engmung/Patternflow/firmware/CUSTOM_PATTERNS.md

# Custom Patterns

Patternflow includes a workflow for creating patterns without writing low-level rendering code. Two paths converge in the same place — the Live Editor at [patternflow.work](https://patternflow.work) → **Pattern** section → **Live Editor**.

- **AI-assisted** — describe the pattern in plain language, paste the AI's output into the editor, tune knobs, copy to C++, flash. No shader knowledge required.
- **Direct** — write the JavaScript pattern by hand in the editor, then convert to C++. For anyone comfortable with fragment-shader-style code.

> **New: you no longer need the Arduino IDE.** The last step — turning a pattern into firmware and getting it onto the board — now runs in the browser: the server compiles, your browser flashes over USB. See [step 5](#5-convert-to-c-and-flash). A local build is still the route for firmware development itself; that is PlatformIO through `firmware/bundles/build.sh`, not the Arduino IDE (the IDE cannot build the editions' library set).

> **Newer still: patterns can install without any flashing at all.** On firmware
> with loadable-module support, the same `.h` builds into a tiny `.pfm` module
> that installs over Wi-Fi from the device's `/patterns` page — a few KB, no
> reflash, no reboot, unlimited slots. The community cart does this end to end.
> Details: [firmware/README.md → Loadable pattern modules](README.md#loadable-pattern-modules-pfm).

The 5-step path below is the AI-assisted route. The direct route reuses the same editor; skip to [Direct coding](#direct-coding-no-ai) if you don't need AI help.

---

## The 5-step path

### 1. Open the Live Editor

Go to [patternflow.work](https://patternflow.work), scroll to the **Pattern** section, and click **Live Editor**. You'll see a 3D preview of the panel on one side and a code editor on the other.

### 2. Copy the creation prompt

Click **Copy creation prompt** above the editor. This copies a prompt that teaches the AI Patternflow's pattern API — the 128×64 grid, the four encoder inputs, the namespace structure, the render call. You don't need to read it. Just paste it.

### 3. Ask an AI for the pattern

Paste the prompt into Claude, ChatGPT, Gemini, or any other code-capable model. At the bottom of the prompt, describe what you want. Examples that have worked well:

- *"A slow vertical aurora — soft greens and purples, gentle wave motion, no hard edges."*
- *"Concentric rings expanding from the center, each ring a slightly different hue."*
- *"Plasma flow that looks like ink in water, deep blues bleeding into magentas."*
- *"A grid of dots pulsing in waves, like a stadium crowd doing the wave."*

The more visual and specific, the better. References to paintings, films, weather, or natural phenomena work well — AI models handle them.

### 4. Paste the JS into the editor

The AI returns JavaScript code. Paste it into the editor pane. The 3D preview updates immediately. The four on-screen knobs and the **ESP32 cost** readout at the top are live.

Turn the knobs to feel how the pattern responds. Adjust constants in the code directly — sensitivity, color ranges, motion speed — until it looks the way you want. This is where you make the pattern yours, not the AI's.

### 5. Convert to C++ and flash

When you're happy with how it looks:

1. Click **Copy C++ prompt**. This bundles your final JS together with a conversion prompt and copies the whole thing to your clipboard.
2. Paste into your AI assistant again. It returns C++ in Patternflow's namespace format.
3. Put it on the device. **Two routes, same result** — pick either:

#### Route A — from the browser (nothing to install, no cable)

In **Pattern Lab**, press **To hardware**, paste the C++ your assistant returned, then press **Apply to my Patternflow**. A server compiles just that pattern into a loadable module (`.pfm`, a few KB, about half a second) and your browser hands it to the board over Wi-Fi. It appears in the pattern list immediately — no reflash, no reboot, no USB.

No Arduino IDE, no board package, no editing `pattern_registry.h`. A community pattern already marked `.h` skips steps 1–2 entirely and offers **Send to my Patternflow**.

Requirements: the device powered on and on the same Wi-Fi as your computer. (Baking a pattern into a whole firmware image used to be the route here; it took fifteen seconds and a cable to do what this does in one, and it is gone. Updating the firmware itself is now its own flow — the device's console tells you when a release is newer and links to [patternflow.work/update](https://patternflow.work/update).)

If the build fails you get the compiler's own error. The usual causes are a helper the firmware already provides being redefined, or a type that differs from the JavaScript original.

#### Route B — a local build (PlatformIO)

1. Save the C++ output as `preset_yourname.h` inside `firmware/patternflow/presets/`.
2. Open `pattern_registry.h` and add two lines (see [Installing your pattern](#installing-your-pattern) below).
3. Build and flash with the bundled toolchain: `./firmware/bundles/build.sh flash patternflow.local` (over Wi-Fi) or `cd firmware/patternflow && pio run -t upload` (USB).

Still the route for changing anything beyond a pattern — firmware development, config edits, working offline, or building for a board you cannot plug into this machine.

> Install the ESP32 board package at **2.0.x**, not the latest 3.x: the newer core takes ~71 KB more internal RAM before your sketch starts, which is enough to stop large patterns loading. `firmware/patternflow/platformio.ini` pins the right core and installs the libraries for you (`cd firmware/patternflow && pio run -t upload`). See [firmware/README.md](README.md#required-board-package).

Long-press encoder 4 on the device to cycle to your new pattern.

> Route B flashes a **whole firmware image**, replacing the firmware and the presets compiled into it; Route A installs a module and touches nothing else. Any `.pfm` modules you've installed live on a separate FATFS partition and **survive a normal reflash** — they only go away if you enable *Erase All Flash Before Sketch Upload*, or format the partition from `/patterns`.

---

## The cost score, explained

At the top of the editor:

```
ESP32 cost: MEDIUM · score 16 · per pixel: trig 4, pow 0, sqrt 0, atan2 0
```

This counts expensive math operations in your pixel loop:

- **trig** — `sin`, `cos`, `tan` calls. Each adds real CPU cost per frame.
- **pow** — exponentiation. Expensive.
- **sqrt** — square root. Expensive.
- **atan2** — angle from x/y. The single most expensive common operation.

**The score is a signal, not a verdict.** It flags patterns that *might* slow down, but the actual frame rate depends on more than this count — loop structure, branching, how the ESP32's cache responds to your access pattern. In practice some patterns with high scores run smoothly, and some with moderate scores stutter unexpectedly.

The rough shape from experience: scores under 20 are reliably smooth. Patterns with truly heavy per-pixel math — stacked `sqrt`, multiple `atan2`, large `pow` — are where slowdowns reliably appear, typically well above score 50. Between those two zones, run it and see. The 3D preview in the browser is a hint, but the only honest test is on the device.

If your score climbs higher than you'd like, the most common fix is moving expensive math *out* of the pixel loop — a `sin` that depends only on time (not on x or y) can be computed once per frame and reused for all 8,192 pixels, and anything that depends only on x, y, or a constant can be precomputed into a lookup table in `setup()` and indexed in `draw()`. Tables are the cheap resource here: measured on hardware, static tables from 0 to 64 KB all render at the same frame rate — and on one real soliton pattern, replacing two `cosh` calls per pixel with a 4 KB table took it from 18 to 33 fps. You can also tell the AI directly: *"Keep cost score under 30. No `atan2`."* Models follow these constraints if you state them in the prompt.

One class of pattern deserves a note because it used to look impossible: anything built on `cosh`/`sinh`/`erf` (solitons, gaussian falloffs) failed to *load* on firmware before v3.5.2 — not slow, refused, with `unresolved symbol` in `loadError`. Those names all resolve now, and the build tooling catches any future gap before a pattern reaches a device. If a pattern of yours was written off as too heavy for the board, try it again on current firmware.

Note that the score measures the *JavaScript* as written — the C++ conversion prompt ships a decision table of firmware fast paths (precomputed per-pixel radius/angle tables for fixed-center patterns, `PFMath::fastAtan2`, cell-hash and pow LUTs), so a HIGH-scoring radial pattern often converts to cheap C++ anyway. Treat the score as pressure, not a wall.

---

## Installing your pattern

Drop the generated header file into the firmware folder:

```
firmware/patternflow/
├── patternflow.ino
├── config.h                   ← hardware pins / display / limits / LED calibration
├── net_config.h               ← Wi-Fi / OTA defaults (+ feature tuning defaults)
├── patternflow_secrets.example.h  ← copy to patternflow_secrets.h for credentials
├── pattern_registry.h         ← edit this
├── _TEMPLATE.h                ← starting point for a new preset
├── presets/                   ← the curated patterns; 35 files, all named preset_*.h
│   ├── preset_origin.h        ← the one compiled into firmware.bin
│   ├── preset_wave_saw.h      ← …the rest ship as the Basics pack (web/public/packs/)
│   ├── preset_0510.h  …
│   └── preset_yourname.h      ← drop your file here
├── abi/                       ← what a .pfm module is compiled against
├── features/                  ← OSC, audio, MQTT, shows… — not the core's business
├── console/                   ← the device's web pages as plain HTML
└── src/                       ← the foundation every pattern draws through
    ├── core_display.h
    ├── core_encoders.h
    ├── core_canvas.h          ← every new pattern draws through this
    ├── core_math.h            ← shared sin LUT + fast trig + fastAtan2
    ├── core_color.h           ← shared HSV/ramp/pow-LUT helpers
    ├── core_noise.h           ← shared Perlin/value noise + cell hash
    ├── core_tables.h          ← precomputed per-pixel radius/angle tables
    ├── core_mem.h             ← PSRAM-first allocator for big buffers
    ├── core_module_loader.h   ← runs .pfm modules off FATFS
    ├── core_wifi.h            ← shared Wi-Fi bring-up
    ├── core_http.h            ← the one port-80 web server
    └── core_web_update.h      ← wireless flashing from the browser
```

A pattern living in `presets/` reaches the foundation one level up — `#include "../src/core_canvas.h"` — which is what `_TEMPLATE.h` describes.

The `src/` folder holds the foundation: generated patterns include the ones they need (`#include "src/core_canvas.h"`, etc.) and call helpers like `PFMath::fastSin`, `PFColor::hsvToRgb`, `PFCanvas::setPixel`. Pattern Lab's "Copy C++ prompt" already teaches the LLM to use these — you should not need to edit the generated file by hand.

Open `pattern_registry.h` and add two things:

```cpp
#include "src/core_encoders.h"
#include "presets/preset_origin.h"
#include "presets/preset_yourname.h"   // ← 1. include your header

// ...

PatternEntry presetPatterns[] = {
  PATTERN_ENTRY(Origin),
  PATTERN_ENTRY(YourNamespace),        // ← 2. add the namespace
};
```

`YourNamespace` is whatever name the AI gave the C++ namespace during the conversion step. It's at the top of your generated `preset_yourname.h`. Match it exactly — C++ is case-sensitive and won't compile if it's off.

Every compiled-in preset costs internal DRAM the web console needs (that is why the registry ships Origin alone — the comment above `presetPatterns[]` has the numbers), so compile in one or two, not thirty.

Build and flash with the bundled toolchain — `./firmware/bundles/build.sh flash patternflow.local` sends the default firmware to the panel over Wi-Fi (`build.sh all` if you touched anything under `src/`). The device picks up the new pattern on the next boot.

---

## The Live Editor in detail

### Buttons

- **Copy creation prompt** — for starting a new pattern. Copies the API spec along with a slot for your description.
- **Copy C++ prompt** — for converting a finished JS pattern. Copies your current code together with a conversion instruction set.

### Knobs

Four knobs corresponding to the four physical encoders. Their labels (Speed, Hue, Density, etc.) are defined by the pattern itself — you, or the AI, decide what each one controls. The labels you set in JS carry through to the C++ namespace and become the on-device readout.

### 3D preview

The preview renders the panel as it would appear on hardware, including aspect ratio (128 × 64) and brightness curve. It's a strong approximation, not a perfect match — colors on the physical HUB75 panel are slightly more saturated, and dark values look darker because the panel has no backlight bleed. Don't fine-tune to pixel-perfect in the preview; tune until it's *close*, flash, then make final adjustments on the device.

---

## Tips for better AI prompts

**Visual references travel well.** "Late-evening ocean ripples, color of bismuth" gives the AI specific direction. "Cool pattern" gives it nothing. Painters, films, natural phenomena, photography references — all of these load specificity into the model.

**Talk about motion and timing.** Color is half of a pattern; motion is the other half. "Slow drift, breathing rhythm, never stops fully" is more useful than just describing colors. "Snappy", "syrupy", "pulsing on the beat" — these all translate.

**Constrain when you need to.** "Stay under cost score 30. No `atan2`. Use additive blending only." Models follow stated constraints if you put them in the prompt. Use this when you've been bitten by a slow pattern once and don't want to be bitten again.

**Iterate in the editor, not in the AI.** Once you have working JS, tweak constants and conditions in the editor pane directly — the 3D preview updates instantly. Going back to the AI for every small tweak is slow, and the AI tends to "redesign" rather than "adjust," which costs you the version you liked.

**If you get stuck, name what's wrong.** "The motion is too fast" or "the contrast is too low" or "I want it to fade in instead of jumping in" — these are useful follow-ups. Vague feedback ("make it better") usually makes it worse.

---

## Direct coding (no AI)

If you want to write the JS yourself, open the Live Editor and start. The minimal pattern looks something like:

```js
function render(x, y, t) {
  const v = 0.5 + 0.5 * Math.sin(t + x * 0.1);
  return hsv(v, 1, 1);
}
```

`x` and `y` are pixel coordinates (0 to 127, 0 to 63). `t` is time in seconds. Knob values and helper functions are available — refer to the prompt copied by **Copy creation prompt** for the full API. That prompt is the canonical reference; this README only summarizes the workflow around it.

The conversion path is the same: tune until you like it, click **Copy C++ prompt**, paste into an AI, save the result as a `presets/preset_*.h` file, register it.

---

## Share what you make

If your pattern is good, publish it.

- **Community** — from the Pattern Lab, click **Publish** and it goes on the [community wall](https://community.patternflow.work/community) under the license you pick, playable by every Patternflow. This is where patterns live; the repository does not take pattern pull requests.
- **Discord** — show it off in the patterns channel: [discord.gg/Vr9QtsxeTk](https://discord.gg/Vr9QtsxeTk)
- **Instagram** — DM Patternflow with a clip and it can get featured

The Patternflow pattern library belongs to the people who actually make patterns, not just the people who designed the hardware.

---

The whole loop, from "I want something like a slow blue wave" to that thing rendering on your physical panel, takes about ten minutes the first time and under five after that.
