engmung/Patternflow/web/content/pattern.md

---
title: Make and flash patterns.
subtitle: Write it here, watch it on the device, flash it from the browser.
status: live
---
