engmung/Patternflow/SUPPORT.md

# Getting help

One table for "where do I ask". Issues are for things that change this repository; everything else has a faster place.

| I want to… | Go to |
| :--- | :--- |
| Get unstuck building, soldering or flashing | [Discord → hardware-help](https://discord.com/channels/1497757947827327067/1499907910707187833) — photos and quick back-and-forth |
| Show a pattern I made, or get feedback on one | Publish it from the [Pattern Lab](https://patternflow.work/pattern-lab) to the [Community](https://community.patternflow.work/community), then [Discord → patterns](https://discord.com/channels/1497757947827327067/1499908302962819236) |
| Put my finished build on the [build map](https://patternflow.work/inside) | [Share your build](https://github.com/engmung/Patternflow/issues/new?template=share_build.yml) — or post it in Discord |
| Talk about where the project should go, or find people working on the same direction | [Discord](https://discord.gg/Vr9QtsxeTk) — the dev-log and the project channels |
| Report a bug, a wrong or missing doc, or propose a feature | [New issue](https://github.com/engmung/Patternflow/issues/new/choose) — pick the template |
| Report a security problem | [SECURITY.md](SECURITY.md) — privately, not as an issue |
| Contribute code, hardware files or docs | [CONTRIBUTING.md](CONTRIBUTING.md) |

**If Discord is blocked where you live**, the community site still works for patterns and decks without it, and a bug or a documentation issue here reaches the maintainer the same day. A discussion venue that works everywhere is planned; until it exists, an issue is the fallback for a question too.

There is no support email. Replies come from the maintainer and from other builders, usually within a day or two.
