engmung/Patternflow/hardware/case/legacy_lasercut/README.md

# legacy_lasercut/

The two laser-cut acrylic drawings from before the printed enclosure existed, kept for the record.

| File | What |
| :--- | :--- |
| `patternflow_v1.svg` | The first case: flat acrylic plates around the v1 board (2026-04). |
| `patternflow_v2.svg` | The same idea cut for the v2.x board (2026-05). |

Both are the maintainer's, CC BY-SA 4.0, drawn for 3 mm acrylic. Neither fits the v3 board, and neither is maintained: the acrylic route was set aside when the printed enclosure became the standard build, and the one attempt to revive it ([#123](https://github.com/engmung/Patternflow/issues/123)) stopped on a dimensioning error.

A new laser-cut variant is welcome — as a remix in [`../remixes/`](../remixes/README.md), not as an edit here.
