engmung/Patternflow/hardware/case/remixes/mbchars-horizontal-desktop-printed/bom.md

# Bill of materials changes

Use these changes with the original [v3.0 BOM](../../../bom/bom_v3.0.csv). The controller PCB components and LED panel remain unchanged.

## Replacement parts

| Original item | Replacement for this enclosure |
|---|---|
| Original printed enclosure | Parts in the [print table](README.md#print-files) |
| Power bank | External USB-C supply with a 5 V output compatible with the trigger |
| USB cable cut for connection to J4 | Complete USB-C cable, separate trigger module, and two output wires to J4 |

## Additional hardware

| Part | Quantity | Specification or location |
|---|---:|---|
| PDSink 303PDSink01 USB Trigger | 1 | Separate module; output set to 5 V |
| Brass heat-set insert | 25 | M3 thread; 5 mm outside diameter; 5 mm length; 4.5 mm printed pilot |
| Joint bar screw | 8 | M3 × 8 mm, countersunk head; two per joint bar |
| USB retainer screw | 1 | M3 × 8 mm, countersunk head |
| Rear cover screw | 16 | M3 × 8 mm, countersunk head |
| Output wire pair | 1 pair | Module +5 V and GND to controller J4 |

The 25 inserts comprise 16 cover inserts, eight joint bar inserts, and one USB retainer insert.

The enclosure uses 25 M3 screws in total.

Do not substitute the enclosure screws for the panel screws.

## Printed quantities

| Part | Quantity |
|---|---:|
| Outer frame | 1 |
| Inner frame | 1 |
| Control section | 1 |
| Display rear cover | 1 |
| Control rear cover | 1 |
| Joint bar | 4 |
| USB retainer | 1 |
| Stand | 2 |
| Knob | 4 |
| Optional 2 mm alignment pin | 4 |

The four small pins can guide the parts during glue application. Glue and pins are optional; the joint bars provide the connections.
