engmung/Patternflow/hardware/case/remixes/mbchars-horizontal-desktop-printed/stl/knob.stl

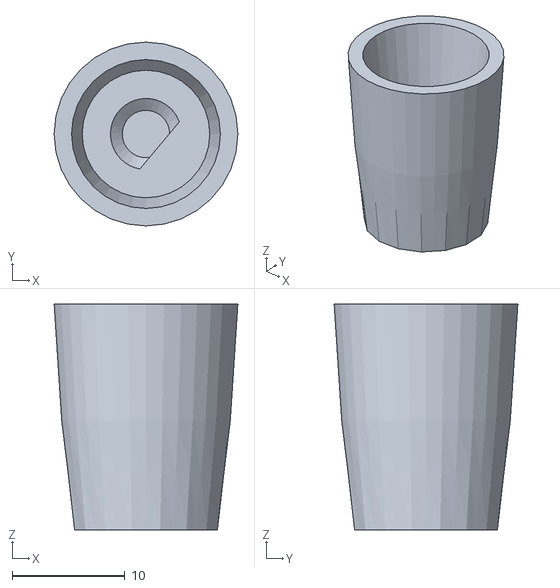
[picture p35: CAD file, 2026-10-10]
hardware/case/remixes/mbchars-horizontal-desktop-printed/stl/knob.stl
16.3 x 16.3 x 20.0
