engmung/Patternflow/hardware/case/bed_256mm/for_other_panels/divided_v3_part1.stl

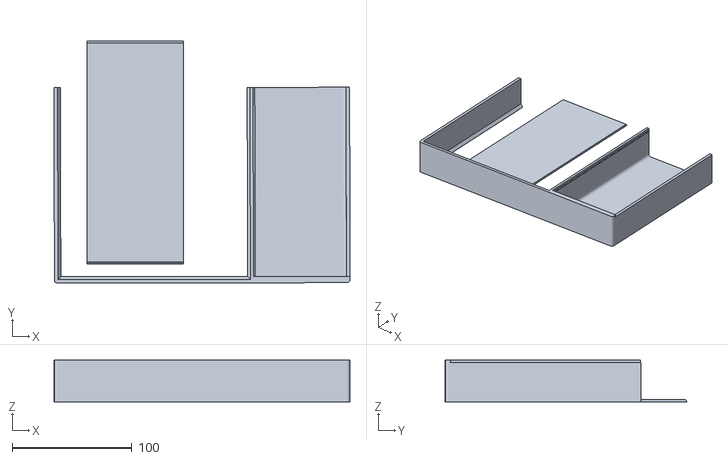
[picture p36: CAD file, 2026-07-08]
hardware/case/bed_256mm/for_other_panels/divided_v3_part1.stl
247.0 x 202.3 x 34.7
