engmung/Patternflow/hardware/case/remixes/mbchars-horizontal-desktop-printed/stl/white_outer_frame.stl

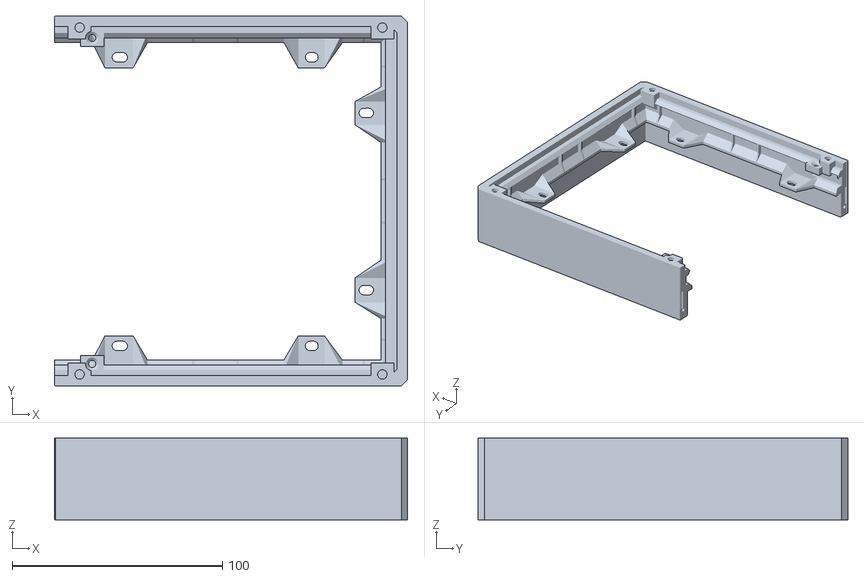
[picture p37: CAD file, 2026-10-10]
hardware/case/remixes/mbchars-horizontal-desktop-printed/stl/white_outer_frame.stl
168.1 x 176.2 x 39.0
