engmung/Patternflow/hardware/case/remixes/mbchars-horizontal-desktop-printed/stl/control_section.stl

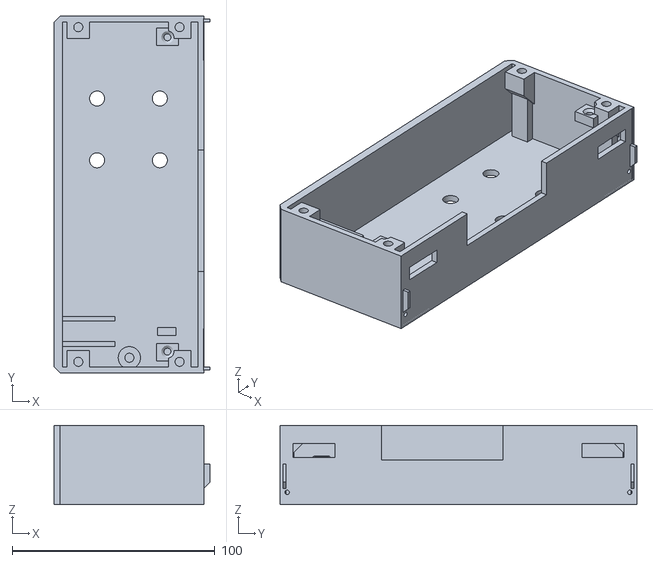
[picture p38: CAD file, 2026-10-10]
hardware/case/remixes/mbchars-horizontal-desktop-printed/stl/control_section.stl
77.0 x 176.2 x 39.0
