engmung/Patternflow/hardware/case/bed_256mm/for_other_panels/divided_v3_part5.stl

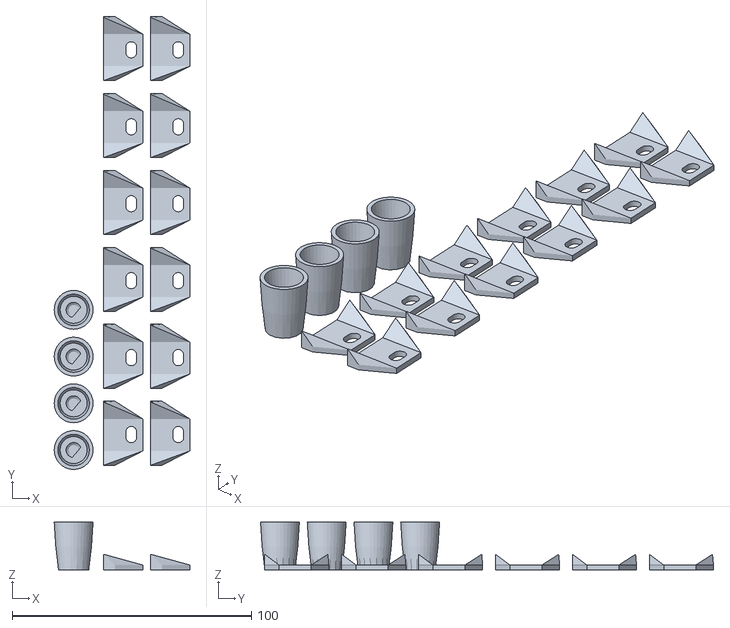
[picture p39: CAD file, 2026-07-08]
hardware/case/bed_256mm/for_other_panels/divided_v3_part5.stl
56.7 x 189.2 x 20.0
