engmung/Patternflow/hardware/case/remixes/mbchars-horizontal-desktop-printed/stl/stand.stl

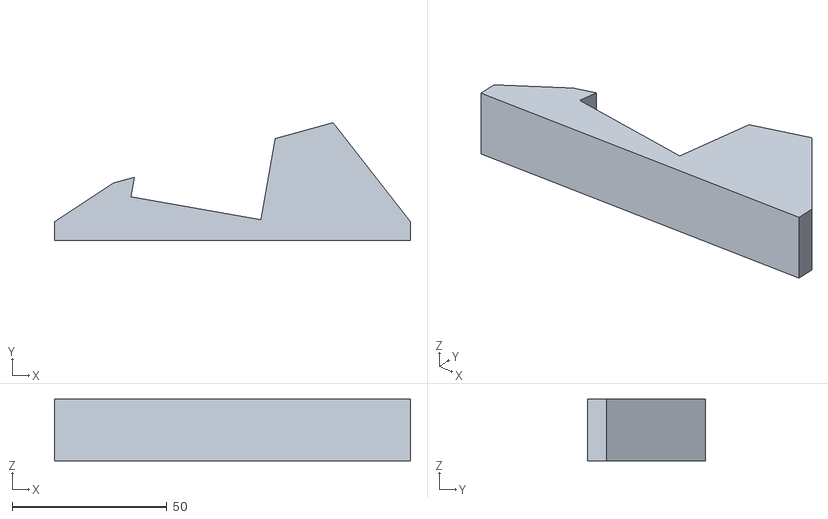
[picture p40: CAD file, 2026-10-10]
hardware/case/remixes/mbchars-horizontal-desktop-printed/stl/stand.stl
115.0 x 38.0 x 20.0
