engmung/Patternflow/hardware/case/remixes/mbchars-horizontal-desktop-printed/stl/white_inner_frame.stl

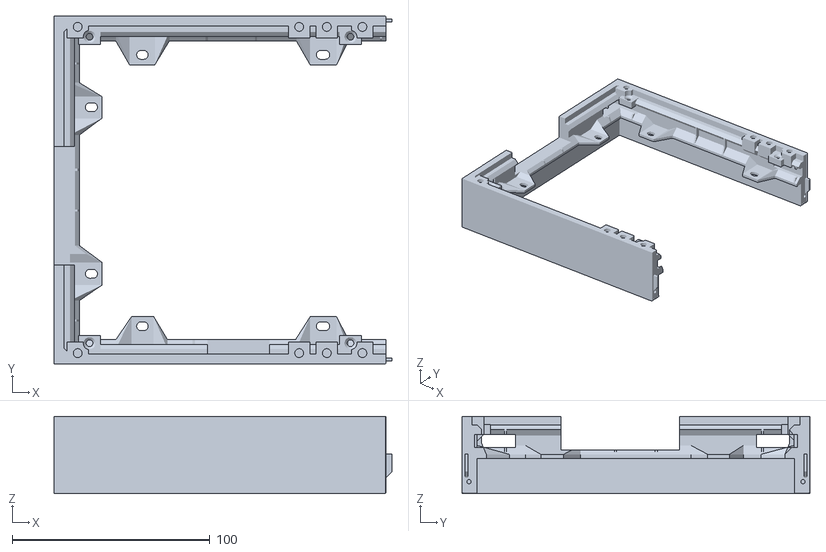
[picture p41: CAD file, 2026-10-10]
hardware/case/remixes/mbchars-horizontal-desktop-printed/stl/white_inner_frame.stl
171.1 x 176.2 x 39.0
