engmung/Patternflow/hardware/case/remixes/mbchars-horizontal-desktop-printed/stl/joint_bar.stl

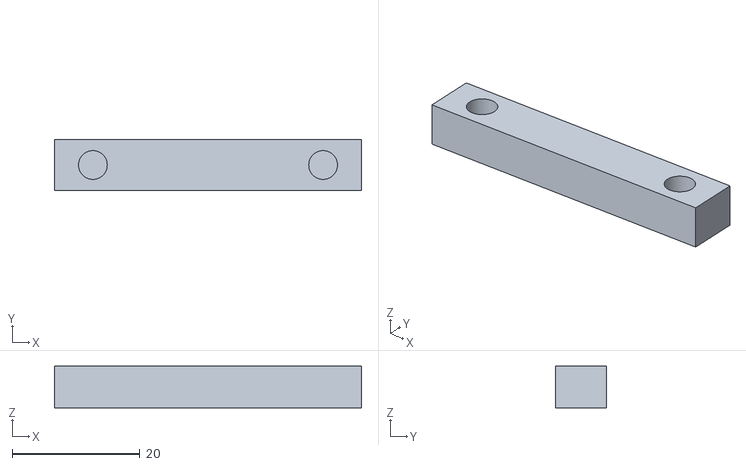
[picture p42: CAD file, 2026-10-10]
hardware/case/remixes/mbchars-horizontal-desktop-printed/stl/joint_bar.stl
48.0 x 8.00 x 6.50
