engmung/Patternflow/hardware/case/remixes/mbchars-horizontal-desktop-printed/stl/alignment_pin_2mm.stl

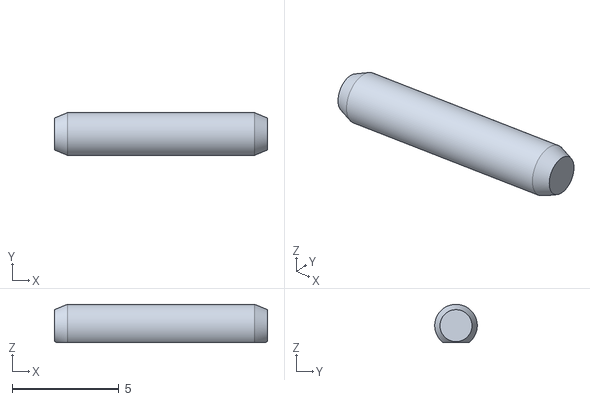
[picture p43: CAD file, 2026-10-10]
hardware/case/remixes/mbchars-horizontal-desktop-printed/stl/alignment_pin_2mm.stl
10.0 x 2.00 x 1.80
