engmung/Patternflow/hardware/case/remixes/mbchars-horizontal-desktop-printed/stl/rear_display_cover.stl

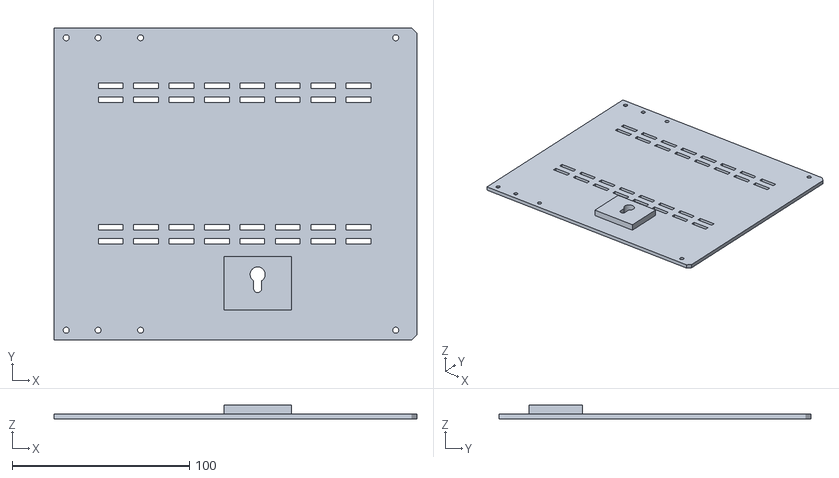
[picture p44: CAD file, 2026-10-10]
hardware/case/remixes/mbchars-horizontal-desktop-printed/stl/rear_display_cover.stl
205.0 x 176.2 x 8.00
