engmung/Patternflow/docs/build-guide/images/v3/05_solder_layout.jpg

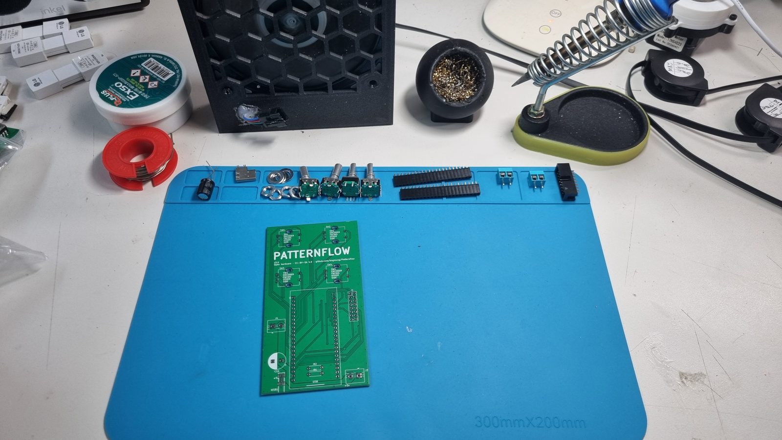
docs/build-guide/images/v3/05_solder_layout.jpg
