engmung/Patternflow/docs/build-guide/images/v3/10_board_back.jpg

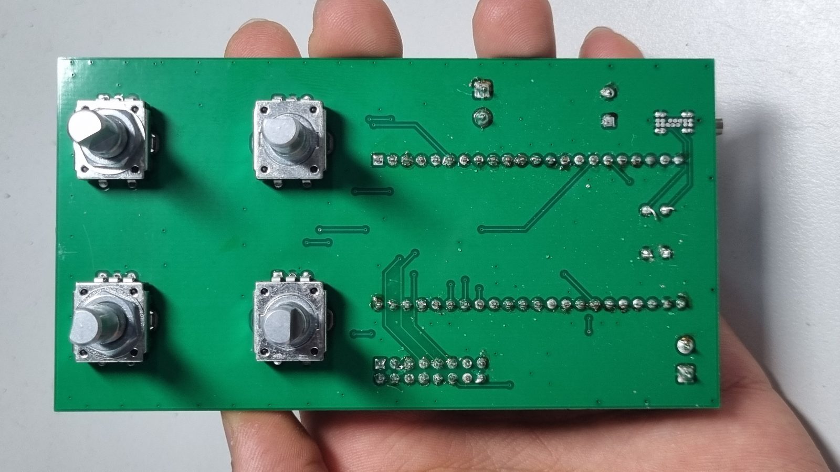
docs/build-guide/images/v3/10_board_back.jpg
