engmung/Patternflow/docs/build-guide/images/v3/11_ready_to_mate.jpg

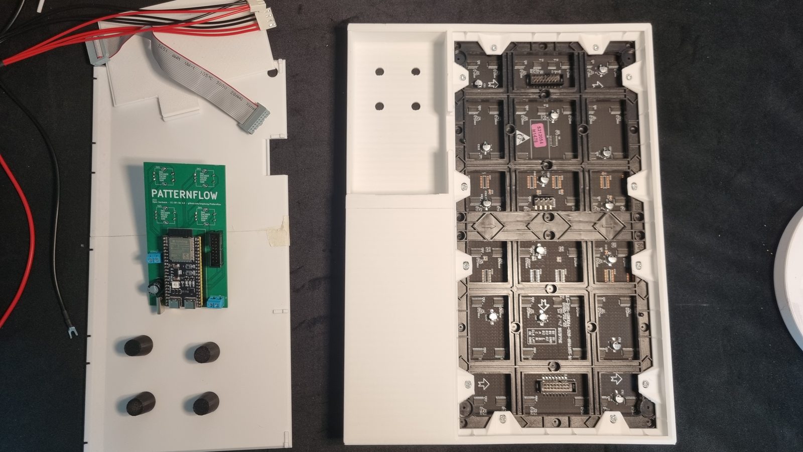
docs/build-guide/images/v3/11_ready_to_mate.jpg
