engmung/Patternflow/docs/build-guide/images/v3/12_hub_in_up.jpg

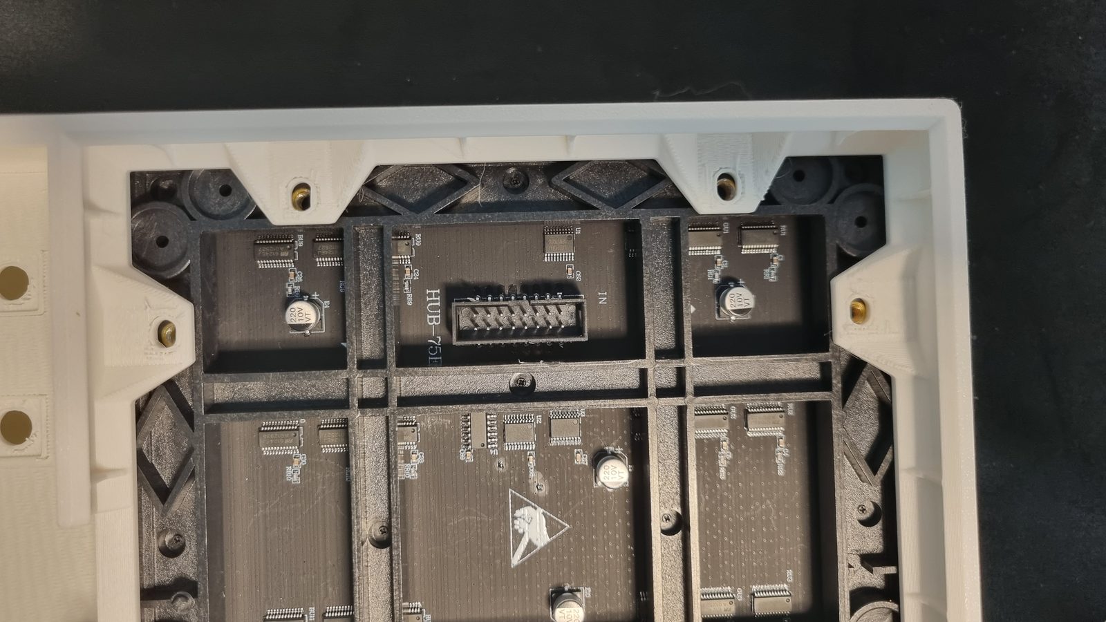
docs/build-guide/images/v3/12_hub_in_up.jpg
