engmung/Patternflow/docs/build-guide/images/v3/13_mount_screws.jpg

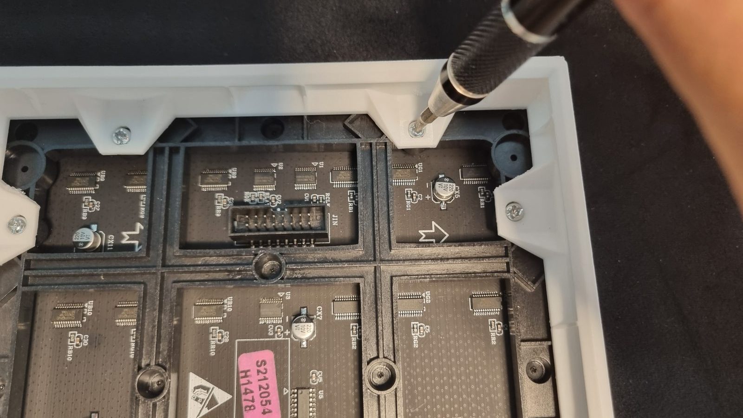
docs/build-guide/images/v3/13_mount_screws.jpg
