engmung/Patternflow/docs/build-guide/images/v3/14_wiring.jpg

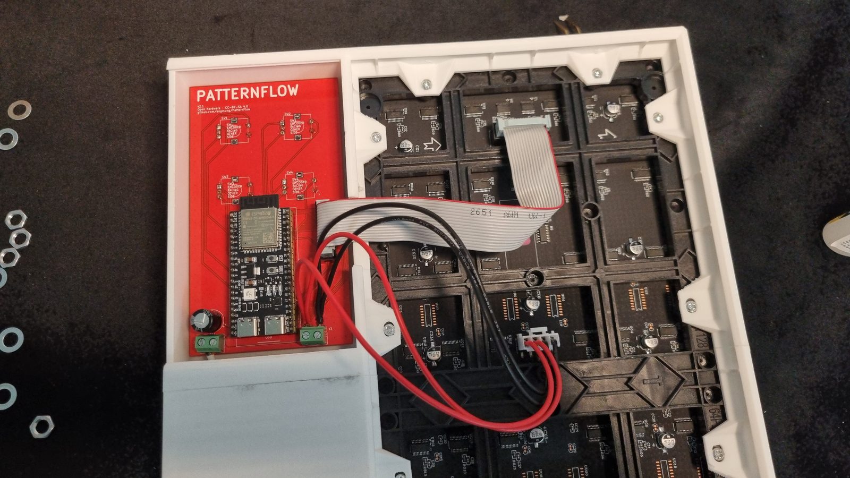
docs/build-guide/images/v3/14_wiring.jpg
