engmung/Patternflow/docs/build-guide/images/v3/15_close_back.jpg

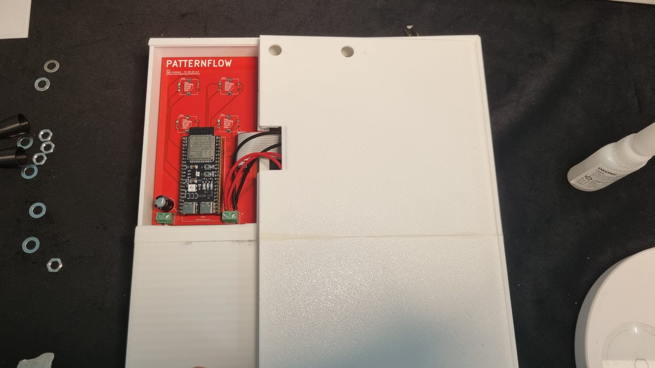
docs/build-guide/images/v3/15_close_back.jpg
