engmung/Patternflow/hardware/pcb/gerber/experiment/README.md

# Experimental Gerbers — do not order

Files in this folder are **unverified, in-development board revisions**. They have not been fabricated and validated yet.

**Do not send these to a fab.** For a working board, order [`../patternflow_v3.9_gerber.zip`](../) — the current recommended revision.

| File | Status |
|---|---|
| *(none right now)* | The v3.0 test board graduated: fabricated, assembled, and verified in [issue #114](https://github.com/engmung/Patternflow/issues/114). It now lives one folder up as `patternflow_v3.0_gerber.zip`. |
