engmung/Patternflow/web/content/journal/i-hope-it-works-out.mdx

---
title: "잘 되면 좋겠다"
date: "2026-07-18T00:30:00+09:00"
excerpt: "할 수 있는 게 기도뿐이라"
cover: "/journal/i-hope-it-works-out/crowd-supply-subscribers.png"
coverCaption: "크라우드 서플라이 구독자 수 그래프"
hideCover: true
draft: false
---

3일 동안 패턴플로우를 소개하는 2분짜리 짧은 영상을 만들었다. 크라우드 서플라이 런칭에도 사용할 영상이며, 유튜브에서 조회수가 잘 나오길 바라며 만들었다. 게시한 지 하루가 지난 지금 상황을 보았을 때, 그 기대는 처참히 무너졌다. 조회수가 백 단위도 되지 못한다. 썸네일이나 제목이 문제인가. 그럼에도 다행인 점은, 보너스라 생각하고 그대로 올린 인스타 영상이 나쁘지 않은 성과를 보이고 있다. 덕분에 아주 최악은 면했다.

<figure className="journal-md-figure">
  <iframe width="100%" height="405" src="https://www.youtube.com/embed/BPMhTChY9vg" title="패턴플로우 소개 영상" allow="accelerometer; autoplay; clipboard-write; encrypted-media; gyroscope; picture-in-picture; web-share" allowFullScreen />
  <figcaption>3일 동안 만든 패턴플로우 소개 영상.</figcaption>
</figure>

오늘 깃허브 스타 수 200개를 넘겼다. 생각보다 늦었다. 내 체감으로는 최근 일주일 동안 스타 수 증가세가 아예 멈추었었다. 무언가 벽을 마주한 기분이었고, 그건 크라우드 서플라이 프리런칭도 마찬가지였다. 지금은 새로운 영상 덕분에 조금 늘어 93명이 되었다. 다음 단계인 런칭을 준비하기 위한 150명 중 1/3 정도가 남은 셈이다. 빠르게 채울 수 있을지는 미지수다. 바람으로는 한 달 안에 채우고 싶은데, 증가세가 주춤해지고 있는 게 보여서 자신이 없다.

<figure className="journal-md-figure">
  크라우드 서플라이 구독자 수 그래프
  <figcaption>크라우드 서플라이 구독자 수 그래프. 93명, 150명까지 1/3 정도가 남았다.</figcaption>
</figure>

그래도 할 수 있는 것들을 해가고 있다. 그 노력의 일환으로 영상을 제작한 것이고, 모바일에서의 CTA도 조금 수정했다. 펀딩 참여를 유도하기 위해 과거에 추가했던 장치가 오히려 역효과를 일으키고 있는 건가 싶어 없앴다. 원래는 이렇게 감으로 하면 안 되고, 테스트를 전부 하고 데이터로 해야 함을 알지만 너무 귀찮다. 아니, 귀찮은 게 아니라 못하는 거다. 그럴 에너지가 없다. 다른 걱정들과, 이를 없애기 위한 발버둥에 쓰기에도 부족하다.

프로젝트 소개 영상을 만들고 나니, 그동안 미뤄왔던 문서화 작업을 시작하게 됐다. 사실 미뤄왔다기보다는 확신이 없었다. 테스트하고 고치고 실패하고 다시 개선하고를 반복하다 보니 고쳐야 할 부분들만 보인다. 문서화를 조금 해보니까 이 정도도 충분하다는 느낌을 받았다. 아니다. 충분하지 않다. 그럼에도 그냥 하는 거다.

패턴플로우가 어느 정도 오픈소스로서 기능을 하고 있다고 느낀다. 우선 직접 만들고 있는 사람들이 꽤 생겼고, 기기뿐만 아니라 아예 새로운 프로젝트의 발화점이 되기도 했다. 다른 사람들이 자신만의 것을 창작하기를 바라는 마음에서 시작한 것이라, 그만큼 많은 변형이 일어난 프로젝트가 내게 더욱 고무적이다. 좋다. 다들 그렇게 자신만의 것을 만들어서 알려주면 좋겠다. 그럴 때 내가 그래도 잘 하고 있구나 라는 안심이 든다.

누군가는 패턴플로우를 사업화해서 판매해도 되냐고 물어보더라. 당연히 된다. 물론 현재 단계에서, 내가 공유해둔 자료들을 기반으로 그대로 만들어 판매하는 건 안 된다. 그 이유는 크라우드 서플라이와의 계약에 선판매 금지 조항이 있기 때문이고, 한번 배치가 끝나고 나면 그것도 가능하다. 당연히 대량 판매의 경우엔 나와 이야기를 하고, 필요시 라이선스 계약 비슷하게 해야 한다. 소량이더라도 나에게 이렇게 미리 알려주고 하는 건 예의이고. 다만 이를 강제하거나 판매하는 걸 막을 생각은 없다. 아니, 나는 솔직히 오히려 좋다. 패턴플로우 사용자가 더 많이 늘어난다는 거니까. 결국에 나는 기기를 파는 게 아니라 한 생태계를 만드는 게 목표기에, 내가 해야 할 일을 누군가 대신 해주는 거다. 거기서 생기는 이익은 당연히 그 사람의 노력에 대한 대가인 것이고.

몇몇 미술관에서 패턴플로우를 구매하고 싶다는 연락도 왔다. 하나같이 똑같다. 자신들의 예산이나 구매 가격을 알려주지 않고 나에게만 제시하라고 한다. 그러곤 그만한 돈이 없다고 깐다. 진짜 개짜증난다. 협상이 아니라 평가당하는 기분이고, 이메일로 소통하는 기간도 길어서 그 기간 동안 불확실성이 나를 메마르게 하더라. 몇 가지를 확실하게 해두어야겠다. 우선 패턴플로우를 대표할 수 있는, 맨 처음 만들었던 이젠 소장용이 된 첫 번째 모델. 사려면 100만 달러다. 사실상 팔지 않겠다는 거다. 그리고 에디션의 경우에는, 가격을 선제시하지 않는다면 무시해야겠다.

짜증난다. 요즘 인간관계에서도 스트레스가 많다. 다른 사람의 행동을 도무지 이해할 수 없다. 차라리 아예 접점이 없었다면 이렇게 신경 쓰지도 않았을 테다. 그래선 안 된다는 걸 알지만, 다른 사람이랑 친해지기가 무서워지고 있다. 아 모르겠다. 그냥 정신병 같다.

계속 해야지. 뭐가 되건 일단은 해야 한다. 그 결과가 좋을지 나쁠지는 모른다. 그저 좋기를 기도할 뿐이다. 종교를 좀 알아볼까? 평생 무신론자였는데, 종교가 생긴다면 어쩌면 인생이 더 편할 수 있을 거라 느껴진다. 나보다 더 큰 무언가를 만들고 믿는다면 쓸데없는 걱정의 절반 정도는 사라지지 않을까. 건강하게 오래 살고 싶다. 신체적으로는 꾸준히 운동하고 좋은 걸 먹고 잘 자면 되는데, 아 잘 못 자고 있긴 하구나. 어쨌든 내가 통제할 수 있다. 반면 정신적으로는 도저히 통제가 안 된다. 스트레스가 만병의 근원이라는데, 이렇게 살다간 젊어서 단명할 것만 같다. 이렇게 생각하니 살기 위해선 뭐라도 조치를 취해야겠다 느껴진다. 심리상담의 경우에는 수차례 해봤지만 크게 개선된 바가 없고, 뭐 연애를 하면 된다 하는데 그것도 어려워 보이고. 결국엔 남아 보이는 게 종교다. 근데 개인적으로 종교가 달갑진 않아서 모르겠다. 아, 명상이나 다시 해볼까.
