engmung/Patternflow/firmware/patternflow/features/audio/core_audio_ws.h

// Patternflow - Audio-react WebSocket server (single-threaded)
//
// Owns: the WebSocket on port 81 and the four lanes it writes. Nothing else -
// no page, no HTTP route (the on/off switch's two routes are in
// feature_audio.h, on the console's server).
//
// This used to serve a page at /audio too — file, tab and microphone capture
// in the browser. It could never work: the device is plain HTTP on a LAN
// address, which is not a secure context, so `navigator.mediaDevices` is not
// merely blocked but absent. Microphone and tab capture were buttons that
// could only ever apologise, and a file player is beside the point when the
// whole value is being in sync with what is actually playing.
//
// Sound reaches a panel two ways now, and neither is that page: a client that
// can capture audio where it is playing (the Chrome extension, which has an
// extension context and can capture a tab; the phone capture app), and the
// on-board microphone in audio_in, which involves no client at all. This
// file is the first kind's way in. A client connects, does its own analysis
// and mapping, and sends each knob a normalized 0..1 value; patterns read
// those through InputFrame::knobAudioActive / knobAudioValue.
//
// Threading: everything runs in the main Arduino loop via handle(). An
// earlier version pushed this into a pinned core-0 FreeRTOS task guarded by
// a portMUX spinlock; that shared the WiFi/lwIP core and could wedge the
// render loop (interrupt watchdog) the moment a client connected. Serving
// inline is simpler and robust — the messages are tiny, so the per-frame
// cost is negligible.
//
// Message protocol (the contract is docs/audio-ws-spec.md; this is a copy):
//   a=F,F,F,F all four lanes at once; '-' leaves a lane alone
//   k=N,v=F   set knob N (0..3) to value F (clamped to 0..1)
//   d=N,v=F   add normalized delta F to knob N (-1..1). Nothing in this tree
//             sends it any more; it is in version 1 of the written contract
//             and earlier extensions spoke nothing else, so it stays.
//   off=N     release knob N back to encoder control
//   off       release all four knobs
//
// A lane holds for AUDIO_TIMEOUT_MS after its last message and is then handed
// back to the encoder. That is what covers a tab closing mid-track - and it
// means a client holding a steady value has to keep saying it.
//
// `a=` exists because sending four `k=` messages per frame did not work. A
// browser client checks `bufferedAmount` before each send so it cannot
// outrun a one-connection server, and after the first send of a frame that
// is never zero - so lanes 1..3 were dropped every frame, in index order,
// and lane 3 never moved at all. One message per frame instead of four: no
// ordering to lose to, and a quarter of the traffic.
//
// Library dependency: WebSockets by Markus Sattler (Links2004).
// WebServer is part of the ESP32 Arduino core.
//
// License: MIT
#pragma once
#include "audio_config.h"

#include <Arduino.h>
#include "../../config.h"

#if PF_AUDIO_ENABLED
#include <WiFi.h>
#include "../../src/webserver/WebServer.h"  // vendored: fixes the 5 s final-chunk stall (see src/webserver/VENDORED.md)
#include <WebSocketsServer.h>
#include "../../src/core_http.h"
#endif

namespace PatternflowAudio {

#if PF_AUDIO_ENABLED

// Quiet window: if no update arrives for a knob within this many ms, it
// deactivates so the physical encoder regains control (covers a browser
// tab closing mid-track).
constexpr uint32_t AUDIO_TIMEOUT_MS = 500;

inline WebSocketsServer wsServer(PF_AUDIO_WS_PORT);

inline bool initialized = false;
inline bool runtimeEnabled = true;
// Plain (not volatile / no spinlock): only ever touched from the main loop.
inline bool active[4]  = { false, false, false, false };
inline float values[4] = { 0.0f, 0.0f, 0.0f, 0.0f };
inline float pendingDeltas[4] = { 0.0f, 0.0f, 0.0f, 0.0f };
inline float deltaResidual[4] = { 0.0f, 0.0f, 0.0f, 0.0f };
inline uint32_t lastUpdateMs[4] = { 0, 0, 0, 0 };
// Not a counter of our own. A hand-kept one drifts: a client whose TCP dies
// without a close frame is reaped by the library without WStype_DISCONNECTED
// ever reaching us, so the count only ever goes up. A panel sitting idle with
// nothing attached was reporting one connected client. The library already
// knows the truth - ask it.

inline void setKnobValue(int idx, float value, uint32_t nowMs) {
  values[idx] = value;
  active[idx] = true;
  lastUpdateMs[idx] = nowMs;
}

inline void addKnobDelta(int idx, float delta, uint32_t nowMs) {
  pendingDeltas[idx] += delta;
  lastUpdateMs[idx] = nowMs;
}

inline void releaseKnob(int idx) {
  active[idx] = false;
  pendingDeltas[idx] = 0.0f;
  deltaResidual[idx] = 0.0f;
}

inline void releaseAllKnobs() {
  for (int i = 0; i < 4; i++) releaseKnob(i);
}

inline void parseMessage(uint8_t* payload, size_t length) {
  if (length < 3 || length > 63) return;

  char buf[64];
  memcpy(buf, payload, length);
  buf[length] = '\0';

  // "a=F,F,F,F" - every lane in one message. A '-' in a slot means "not
  // driven by this client", which is how a muted band stays out of the way
  // without needing a release of its own.
  if (buf[0] == 'a' && buf[1] == '=') {
    const char* p = buf + 2;
    uint32_t now = millis();
    for (int i = 0; i < 4 && *p; i++) {
      if (*p == '-') {
        p++;
      } else {
        char* end = nullptr;
        float v = strtof(p, &end);
        if (end == p) break;
        if (v < 0.0f) v = 0.0f;
        else if (v > 1.0f) v = 1.0f;
        setKnobValue(i, v, now);
        p = end;
      }
      if (*p == ',') p++;
    }
    return;
  }

  // "k=N,v=F" — parsed by hand (no sscanf: its %f path is needlessly
  // heavy and this runs on every inbound frame).
  if ((buf[0] == 'k' || buf[0] == 'd') && buf[1] == '=') {
    char* end = nullptr;
    long k = strtol(buf + 2, &end, 10);
    if (end && *end == ',' && end[1] == 'v' && end[2] == '=' && k >= 0 && k < 4) {
      float v = strtof(end + 3, nullptr);
      if (buf[0] == 'k') {
        if (v < 0.0f) v = 0.0f;
        else if (v > 1.0f) v = 1.0f;
        setKnobValue((int)k, v, millis());
      } else {
        if (v < -1.0f) v = -1.0f;
        else if (v > 1.0f) v = 1.0f;
        addKnobDelta((int)k, v, millis());
      }
    }
    return;
  }
  // "off=N" — release knob N.
  if (strncmp(buf, "off=", 4) == 0) {
    long k = strtol(buf + 4, nullptr, 10);
    if (k >= 0 && k < 4) releaseKnob((int)k);
    return;
  }
  // "off" — release all four.
  if (strcmp(buf, "off") == 0) releaseAllKnobs();
}

inline void onEvent(uint8_t num, WStype_t type, uint8_t* payload, size_t length) {
  switch (type) {
    case WStype_CONNECTED: {
      IPAddress ip = wsServer.remoteIP(num);
      Serial.printf("[AUDIO] client %u from %s (%d connected)\n",
                    num, ip.toString().c_str(), wsServer.connectedClients());
      break;
    }
    case WStype_DISCONNECTED: {
      // connectedClients() still counts this one - the library frees the slot
      // after the callback returns.
      if (wsServer.connectedClients() <= 1) releaseAllKnobs();
      Serial.printf("[AUDIO] client %u disconnected (%d connected)\n",
                    num, wsServer.connectedClients() - 1);
      break;
    }
    case WStype_TEXT:
      parseMessage(payload, length);
      break;
    default:
      break;
  }
}

#endif  // PF_AUDIO_ENABLED

inline bool isCompiledIn() {
#if PF_AUDIO_ENABLED
  return true;
#else
  return false;
#endif
}

inline bool isActive(int idx) {
#if PF_AUDIO_ENABLED
  if (idx < 0 || idx >= 4) return false;
  if (!runtimeEnabled) return false;
  return active[idx];
#else
  (void)idx;
  return false;
#endif
}

inline float value(int idx) {
#if PF_AUDIO_ENABLED
  if (idx < 0 || idx >= 4) return 0.0f;
  return values[idx];
#else
  (void)idx;
  return 0.0f;
#endif
}

inline int consumeKnobDelta(int idx) {
#if PF_AUDIO_ENABLED
  if (idx < 0 || idx >= 4 || !runtimeEnabled) return 0;
  float movement = pendingDeltas[idx] * PF_LANE_MOTION_SCALE + deltaResidual[idx];
  pendingDeltas[idx] = 0.0f;
  int delta = (int)roundf(movement);
  deltaResidual[idx] = movement - (float)delta;
  if (fabsf(deltaResidual[idx]) < 0.001f) deltaResidual[idx] = 0.0f;
  return delta;
#else
  (void)idx;
  return 0;
#endif
}

inline uint32_t clientCount() {
#if PF_AUDIO_ENABLED
  if (!initialized) return 0;
  int n = wsServer.connectedClients();
  return n > 0 ? (uint32_t)n : 0;
#else
  return 0;
#endif
}

inline bool isRuntimeEnabled() {
#if PF_AUDIO_ENABLED
  return runtimeEnabled;
#else
  return false;
#endif
}

inline void setRuntimeEnabled(bool on) {
#if PF_AUDIO_ENABLED
  runtimeEnabled = on;
  if (!on) releaseAllKnobs();
#else
  (void)on;
#endif
}

// Start the HTTP/WebSocket servers. Wi-Fi is owned by PatternflowWifi; this
// runs on the connect edge. Idempotent — repeat calls (on reconnect) are
// no-ops once the servers are up.
inline void begin() {
#if PF_AUDIO_ENABLED
  if (initialized) return;
  if (!PatternflowWifi::linkUp()) return;

  PatternflowHttp::begin();  // idempotent; whoever is first starts it

  wsServer.begin();
  wsServer.onEvent(onEvent);

  initialized = true;

  // "[AUDIO] Ready" is the literal firmware/bundles/build.sh looks for in an
  // image to prove this feature is in it. Reword the rest, not those two words.
  String ip = WiFi.localIP().toString();
  Serial.printf("[AUDIO] Ready — UI http://%s:%d  WS ws://%s:%d\n",
                ip.c_str(), PF_AUDIO_HTTP_PORT, ip.c_str(), PF_AUDIO_WS_PORT);
#endif
}

// Service the servers + auto-release stale knobs. Called every main loop.
inline void handle() {
#if PF_AUDIO_ENABLED
  if (!initialized) return;

  // A burst, not one call: the library hands over ONE message per loop()
  // pass per client, and the phone sends lanes 20 times a second while
  // HTTP work (page polls, monitor frames) steals main-loop passes. At one
  // message per pass the drain rate dips below the arrival rate, messages
  // back up in TCP, and the panel keeps dancing SECONDS after the music
  // stops - measured, not theorized. Six passes cost microseconds when
  // idle and give the drain a 6x ceiling when it matters.
  for (int k = 0; k < 6; k++) wsServer.loop();

  uint32_t now = millis();
  for (int i = 0; i < 4; i++) {
    if (active[i] && (now - lastUpdateMs[i]) > AUDIO_TIMEOUT_MS) {
      active[i] = false;
    }
    if (pendingDeltas[i] != 0.0f && (now - lastUpdateMs[i]) > AUDIO_TIMEOUT_MS) {
      pendingDeltas[i] = 0.0f;
      deltaResidual[i] = 0.0f;
    }
  }
#endif
}

} // namespace PatternflowAudio
