engmung/Patternflow/firmware/patternflow/features/audio_in/core_audio_pdm.h

// ═══════════════════════════════════════════════════════════
// PatternFlow - the microphone, at last
//
// core_audio_fft.h was written before any microphone existed, because the
// question that decided whether the feature was possible was "is there CPU
// left", not "can we read a mic". That answered yes. This is the other half.
//
// A PDM MEMS mic on the only two free header pins this board has: GPIO43 and
// GPIO44, the UART0 TX/RX pads. They are free because the console runs over
// native USB CDC (USBMode=hwcdc, CDCOnBoot=cdc) and nothing drives UART0.
// Everything else is HUB75, an encoder, or claimed by the N16R8's octal
// PSRAM at 35-37.
//
//   mic 3V   -> 3V3          mic CLK -> GPIO43
//   mic GND  -> GND          mic DAT -> GPIO44
//   mic SEL  -> GND          SEL low = LEFT channel, which is the slot a mono
//                            PDM RX reads. Tie it high instead and this reads
//                            silence while looking perfectly healthy.
//
// ── The neighbours ──────────────────────────────────────────────────────
//
// GPIO43 and GPIO44 are the only unclaimed pins on this board. Everything
// else is HUB75, an encoder, the USB pair, or the N16R8's octal PSRAM at
// 35-37 — 26 of the 28 usable GPIOs, and the two that are left are these.
//
// They are also immediately next to the panel's RGB bus:
//
//     40  B1 ┐
//     41  G1 ├─ HUB75 data, switching at the pixel clock
//     42  R1 ┘
//     43  PDM CLK      <- us
//     44  PDM DAT      <- us
//
// So a 1-bit PDM stream on a flying lead runs alongside three pins carrying
// the panel's picture at MHz rates, which is not where anyone would choose to
// put a microphone.
//
// In practice it is fine. The assembled device reads clean with the panel
// running — the spikes that looked like crosstalk turned out to be a
// backlogged DMA ring, and they went with it. This is recorded because the
// adjacency is real and somebody will wonder, not because it is a known
// fault: if a build ever does show the picture in the audio, short leads away
// from the ribbon are the first thing to try, and a board revision that
// brings the microphone header out away from the panel bus would settle it.
//
// ── Which driver ────────────────────────────────────────────────────────
//
// driver/i2s.h - the legacy one. Not a preference: platformio.ini pins
// espressif32@7.0.1, whose Arduino core is 2.0.17 on IDF 4.4, and that SDK
// ships only tools/sdk/esp32s3/include/driver/include/driver/i2s.h. The
// channel API this was first written against (driver/i2s_pdm.h,
// i2s_channel_read) belongs to IDF 5.x and is not on the include path. If
// this project ever moves to a core built on IDF 5, this file is the one to
// rewrite, and the rewrite is worth doing: the new API is not deprecated and
// its GPIO config names the PDM clock pin `clk` instead of hiding it in `ws`.
//
// Arduino's I2SClass is not used either, and would not be even where it
// exists: readBytes loops `while (total_size < size)` around a read whose
// timeout is Stream's, 1000 ms by default. A mic that is wired wrong returns
// zero bytes forever, so that loop never ends and the analysis task is gone
// for good - no error, no watchdog, just a feature that stopped. i2s_read is
// one attempt with a bounded wait, and a partial read is data, not failure.
//
// The S3 has a hardware PDM-to-PCM filter, so what lands in the DMA buffer is
// already int16 PCM. Nothing here decimates a 1-bit stream.
//
// A silent mic and an absent mic have to be distinguishable, so a run of
// empty reads falls back to the synthetic source and says so at /api/status.
// Otherwise the bands sit at zero and there is nothing to tell you whether
// the room is quiet or the wiring is wrong.
//
// License: MIT
// ═══════════════════════════════════════════════════════════
#pragma once

#include <Arduino.h>

// Set to 0 to build the analysis without ever touching I2S - the measurement
// harness the FFT was originally written for, on a board with no mic.
#ifndef PF_AUDIO_IN_PDM_ENABLED
#define PF_AUDIO_IN_PDM_ENABLED 1
#endif

// Downsample-ratio experiment, CLOSED. DSR_16S doubles the PDM clock
// (fs*64 -> fs*128, 1.024 -> 2.048 MHz at 16 kHz); the hope was a mic whose
// low-power threshold sits near 1 MHz waking up. Measured 2026-08-30 on this
// hardware, same tone, same volume: tone rawPeak 0.0059 (DSR16) vs 0.0052
// (DSR8) - inside run-to-run noise, matching esp-idf#8660's finding - and
// DSR16 dragged the window rate to 56.6/s against DSR8's 60.6. So 8 stays
// the default; the define stays because the experiment cost one flag and the
// next microphone model may answer differently.
#ifndef PF_AUDIO_IN_PDM_DSR16
#define PF_AUDIO_IN_PDM_DSR16 0
#endif

#if PF_AUDIO_IN_PDM_ENABLED
#include <driver/i2s.h>
#if !SOC_I2S_SUPPORTS_PDM_RX
#error "PF_AUDIO_IN_PDM_ENABLED but this chip has no PDM RX"
#endif
#endif

// The two free pads. Overridable because a board that frees different pins is
// a wiring change, not a code change.
#ifndef PF_AUDIO_IN_PDM_CLK
#define PF_AUDIO_IN_PDM_CLK 43
#endif
#ifndef PF_AUDIO_IN_PDM_DAT
#define PF_AUDIO_IN_PDM_DAT 44
#endif

namespace PFAudioPdm {

// Matches PFAudioFFT: a 512-point window at 16 kHz. The hop is half a window,
// so consecutive windows overlap 50% and a transient lands in the frame it
// happened in rather than up to a window late.
constexpr int WINDOW = 512;
constexpr int HOP = WINDOW / 2;
constexpr uint32_t RATE = 16000;

inline bool live = false;      // I2S came up
inline bool stalled = false;   // ...and then stopped producing samples
inline uint32_t windowsRead = 0;
// How many hops have been thrown away because the analysis fell behind. The
// number that says whether this is keeping up; see readWindow.
inline uint32_t dropped = 0;

inline bool available() { return live && !stalled; }

inline const char* sourceName() {
  if (!live) return "synth";
  return stalled ? "synth (mic stalled)" : "pdm";
}

#if PF_AUDIO_IN_PDM_ENABLED

// One hop of audio is 16 ms. 40 ms leaves room for a late DMA buffer without
// being long enough to miss a frame when the mic has gone away.
constexpr uint32_t READ_TIMEOUT_MS = 40;
// Empty reads in a row before we stop believing there is a microphone. Three
// is ~120 ms: long enough that one scheduling hiccup does not trip it.
constexpr int STALL_LIMIT = 3;
// Port 0. The panel is HUB75 on its own peripheral and nothing else here
// wants an I2S port, so there is no allocation to negotiate.
constexpr i2s_port_t PORT = I2S_NUM_0;

inline int emptyReads = 0;
// Two, not one. The drain below keeps only the newest hop, and the window is
// built from the newest plus whatever was in the ring - which after a drain is
// a hop from further back, spliced against it at index WINDOW - HOP. That is
// the exact centre of the window, where the Hann term peaks at 2.0 and
// attenuates the discontinuity by nothing at all. Alternating buffers keeps the
// hop that actually precedes the newest one, so the two halves stay adjacent.
inline int16_t rawA[HOP];
inline int16_t rawB[HOP];

// The ring the window is cut from: the previous hop, then the new one.
inline float ring[WINDOW];

// Installing I2S costs about 7.9 KB of internal heap — measured by building
// the same edition with PF_AUDIO_IN_PDM_ENABLED 0 and comparing one clean
// reading each. That is not much on this board, and it is not the reason
// anybody's console is slow; it is simply rude to spend it on a panel with no
// microphone wired, which is most of them.
//
// So it starts on demand and can be handed back. `begin()` is the install,
// `end()` is the release, and both are safe to call twice.
inline void end() {
  if (!live) return;
  i2s_driver_uninstall(PORT);
  live = false;
  stalled = false;
  emptyReads = 0;
  Serial.println("[AUDIO-IN] PDM released");
}

inline void begin() {
  if (live) return;
  i2s_config_t cfg = {};
  cfg.mode = (i2s_mode_t)(I2S_MODE_MASTER | I2S_MODE_RX | I2S_MODE_PDM);
  cfg.sample_rate = RATE;
  cfg.bits_per_sample = I2S_BITS_PER_SAMPLE_16BIT;
  // SEL tied to GND puts the mic on the left channel; asking for both would
  // interleave 16 ms of real audio with 16 ms of silence.
  cfg.channel_format = I2S_CHANNEL_FMT_ONLY_LEFT;
  cfg.communication_format = I2S_COMM_FORMAT_STAND_I2S;
  // LEVEL1 so the panel's DMA, which is what this device is actually for,
  // keeps priority over the microphone.
  cfg.intr_alloc_flags = ESP_INTR_FLAG_LEVEL1;
  // Four buffers of a hop each: a late analysis task has a whole window of
  // slack before anything is lost.
  cfg.dma_buf_count = 4;
  cfg.dma_buf_len = HOP;
  cfg.use_apll = false;
  cfg.tx_desc_auto_clear = false;
  cfg.fixed_mclk = 0;

  esp_err_t err = i2s_driver_install(PORT, &cfg, 0, nullptr);
  if (err != ESP_OK) {
    Serial.printf("[AUDIO-IN] i2s_driver_install failed (%d) - using synth\n", (int)err);
    return;
  }

  // In PDM RX the clock the mic is driven by comes out of the WS pad, not
  // BCK. Wiring CLK to a pin named bck_io_num here is the mistake to expect:
  // it installs cleanly, produces no samples, and looks like a dead mic.
  i2s_pin_config_t pins = {};
  pins.mck_io_num = I2S_PIN_NO_CHANGE;
  pins.bck_io_num = I2S_PIN_NO_CHANGE;
  pins.ws_io_num = PF_AUDIO_IN_PDM_CLK;
  pins.data_out_num = I2S_PIN_NO_CHANGE;
  pins.data_in_num = PF_AUDIO_IN_PDM_DAT;
  err = i2s_set_pin(PORT, &pins);
  if (err != ESP_OK) {
    Serial.printf("[AUDIO-IN] i2s_set_pin failed on CLK=%d DAT=%d (%d) - using synth\n",
                  PF_AUDIO_IN_PDM_CLK, PF_AUDIO_IN_PDM_DAT, (int)err);
    i2s_driver_uninstall(PORT);
    return;
  }

#if PF_AUDIO_IN_PDM_DSR16
  i2s_set_pdm_rx_down_sample(PORT, I2S_PDM_DSR_16S);
#endif

  for (int i = 0; i < WINDOW; i++) ring[i] = 0.0f;
  live = true;
  // "PDM up: CLK" is the literal firmware/bundles/build.sh looks for in an
  // image to prove this feature is in it. Reword around it, not through it.
  Serial.printf("[AUDIO-IN] PDM up: CLK=%d DAT=%d %luHz mono left dsr=%d\n",
                PF_AUDIO_IN_PDM_CLK, PF_AUDIO_IN_PDM_DAT, (unsigned long)RATE,
                PF_AUDIO_IN_PDM_DSR16 ? 16 : 8);
}

// Read one hop, slide it into the ring, and hand back a whole window.
// Returns false when there was nothing to read, which is the caller's cue to
// fall back rather than analyse a window of silence it invented.
//
// Blocking here is the point: at 16 kHz a hop takes 16 ms to exist, so this
// paces the analysis task against the audio clock.
//
// ── Which is only true while we are keeping up ──────────────────────────
//
// The DMA ring holds four hops, 64 ms. Miss that much — and on the assembled
// device that is easy, with the panel blitting on core 1 and Wi-Fi on core 0 —
// and the ring is full. From then on every read returns INSTANTLY from the
// backlog instead of blocking for 16 ms, the task stops being paced by
// anything, and it spins a 477 us transform back to back at priority 1 on the
// core Wi-Fi lives on. That starves the thing that made it late, which fills
// the ring further. It does not recover.
//
// Reported as: fine for a while, then suddenly bad and stays bad, the console
// stops answering, and only on the real device — never on a bare DevKit with
// no panel to compete with.
//
// So a read is followed by a non-blocking drain: whatever else is queued is
// pulled out and discarded, and the window is cut from the NEWEST hop. Falling
// behind then costs some dropped audio and nothing else, which is the right
// price — the analysis is for reacting to now, and a backlog is by definition
// not now. `dropped` counts it so the condition is visible instead of
// inferred.
inline bool readWindow(float* dst) {
  if (!live) return false;

  int16_t* cur = rawA;
  int16_t* prev = rawB;
  size_t got = 0, prevGot = 0;
  int skipped = 0;
  const esp_err_t err = i2s_read(PORT, cur, sizeof(rawA), &got,
                                 pdMS_TO_TICKS(READ_TIMEOUT_MS));

  // Drain to the newest. Bounded, because a ring that refills as fast as it
  // empties must not turn this into the spin it exists to prevent. Reading
  // alternately into the two buffers costs nothing and leaves `prev` holding
  // the hop immediately before `cur`, which is what the window needs.
  for (int guard = 0; guard < 8; guard++) {
    size_t more = 0;
    int16_t* into = (cur == rawA) ? rawB : rawA;
    if (i2s_read(PORT, into, sizeof(rawA), &more, 0) != ESP_OK || more == 0) break;
    prev = cur;
    prevGot = got;
    cur = into;
    got = more;
    dropped++;
    skipped++;
  }

  const int samples = (int)(got / sizeof(int16_t));
  if (samples == 0) {
    if (++emptyReads >= STALL_LIMIT && !stalled) {
      stalled = true;
      Serial.printf("[AUDIO-IN] no samples from the mic (err %d) - falling back to synth\n",
                    (int)err);
    }
    return false;
  }
  if (stalled) {
    stalled = false;
    Serial.println("[AUDIO-IN] mic is back");
  }
  emptyReads = 0;
  windowsRead++;

  const float k = 1.0f / 32768.0f;

  // Slide: the previous hop becomes the window's first half. Correct as long
  // as nothing was skipped - two consecutive reads ARE adjacent audio.
  for (int i = 0; i < WINDOW - HOP; i++) ring[i] = ring[i + HOP];

  // If hops were dropped, what just slid in is not adjacent to what follows it.
  // Overwrite it with the hop that is. Simulated at N=512 with the shipped
  // window, one splice at the centre lifts the upper bands by a factor of a few
  // against the contiguous window from the same instant - and it lands in an
  // envelope with an eight-second release, so one backlogged read colours the
  // lanes for seconds. The drain itself is correct and stays; only the seam
  // was wrong.
  if (skipped > 0) {
    const int m = (int)(prevGot / sizeof(int16_t));
    const int pn = m < HOP ? m : HOP;
    for (int i = 0; i < pn; i++) ring[i] = (float)prev[i] * k;
    for (int i = pn; i < HOP; i++) ring[i] = 0.0f;
  }
  // int16 full scale to roughly +/-1, and nothing else: no gain here. The
  // real number the silicon returned has to survive to the diagnostics
  // (rawPeak/rawDc are documented as raw) and to the dead-rail check. The
  // user-tunable microphone gain is applied downstream in analyze(), after
  // those are measured from the same window.
  const int n = samples < HOP ? samples : HOP;
  for (int i = 0; i < n; i++) ring[WINDOW - HOP + i] = (float)cur[i] * k;
  // A short read leaves the tail of the hop holding the previous window's
  // audio. Zero it instead: repeating 16 ms of sound is a spectral artefact,
  // silence is only quieter.
  for (int i = n; i < HOP; i++) ring[WINDOW - HOP + i] = 0.0f;

  for (int i = 0; i < WINDOW; i++) dst[i] = ring[i];
  return true;
}

#else  // PF_AUDIO_IN_PDM_ENABLED

inline void begin() {}
inline bool readWindow(float*) { return false; }

#endif

}  // namespace PFAudioPdm
