engmung/Patternflow/firmware/patternflow/features/audio_in/feature_audio_in.h

// ═══════════════════════════════════════════════════════════
// PatternFlow - on-board audio input, as a feature
//
// Owns: the descriptor, the analysis task, and the one place sound becomes
// knob lanes (fillInput). The parts it wires together each own one thing:
//
//   core_audio_pdm.h      the microphone - a PDM MEMS part on GPIO43/44
//   core_audio_fft.h      a window of samples -> spectrum -> four band levels
//   core_audio_in_map.h   a band's level -> its knob; the settings and NVS
//   core_audio_in_http.h  /audio-in and /api/audio-in
//
// It was the first feature written on the seam rather than moved onto it, and
// it needed no core edit. The hooks it uses:
//
//   setup        - load the settings, build the FFT tables, start the task
//   onNetwork    - register the page and its API
//   fillInput    - four bands drive the four knob lanes, exactly the way
//                  the weather feature drives them from a temperature. A
//                  pattern animates from sound without knowing what sound is.
//   appendStatus - the `audioIn` block: what the analysis costs, and what the
//                  microphone is returning
//
// PF_AUDIO_IN_CORE picks who pays for the analysis:
//   0  a task pinned to Core 0, where Wi-Fi lives and the panel does not.
//      What ships.
//   1  the render loop (Core 1), inline through the loop hook. Kept for
//      measuring that placement against the other; no edition builds it.
//
// The analysis was written and costed before there was a microphone - the
// panel spends ~10 ms of every 16.6 ms frame pushing pixels, and if a
// spectrum had not fitted in what is left no microphone would have helped.
// It fitted. The synthetic source that stood in for the microphone then is
// still in core_audio_fft.h, and is what the analysis runs on when the
// microphone is not delivering; see fillInput for why it stops there.
//
// License: MIT
// ═══════════════════════════════════════════════════════════
#pragma once

#include "../pf_feature.h"
#include "core_audio_fft.h"
#include "core_audio_in_http.h"
#include "core_audio_in_map.h"
#include "core_audio_pdm.h"

#ifndef PF_AUDIO_IN_CORE
#define PF_AUDIO_IN_CORE 0
#endif

// Off unless the composition says so: carrying this feature to measure it, or
// to watch the page, must not move anybody's knobs. The Audio edition turns
// it on in its overrides.h.
#ifndef PF_AUDIO_IN_DRIVES_KNOBS
#define PF_AUDIO_IN_DRIVES_KNOBS 0
#endif

namespace PFFeatureAudioIn {

inline uint32_t tick = 0;
inline uint32_t heapCost = 0;

#if PF_AUDIO_IN_CORE == 0
inline void analysisTask(void*) {
  for (;;) {
    // With the microphone off there is nothing to analyse and no reason to
    // wake 60 times a second on the core Wi-Fi lives on. The task stays
    // parked; flipping the switch on /audio-in starts I2S and it resumes.
    if (!PFAudioInMap::micOn) {
      if (PFAudioPdm::live) PFAudioPdm::end();
      vTaskDelay(pdMS_TO_TICKS(250));
      continue;
    }
    if (!PFAudioPdm::live) PFAudioPdm::begin();

    PFAudioFFT::analyze(tick++);
    // Envelope tracking rides the analysis clock - once per window, here,
    // never from the mapping (which also runs from HTTP polls and would
    // double-count the release). The gate hears RAW frames (its constants
    // were measured that way); the damped copy is what the mapping and the
    // page consume.
    if (PFAudioInMap::micOn) {
      PFAudioInMap::trackEnvelopes(PFAudioFFT::bands);
      PFAudioInMap::smoothLevels(PFAudioFFT::bands);
    }
    // With a microphone the I2S read paces this loop, and without one nothing
    // blocks at all, so the synthetic path keeps the old 16 ms tick.
    //
    // Either way this ALWAYS yields for at least a tick. It used to
    // taskYIELD() on the microphone path, on the reasoning that the read was
    // the clock - which stops being true the moment the DMA ring backs up and
    // reads start returning instantly. A priority-1 task spinning on the core
    // Wi-Fi runs on is how a panel stops answering, and a yield that cannot
    // guarantee anything is not a floor. One tick is.
    vTaskDelay(PFAudioPdm::available() ? 1 : pdMS_TO_TICKS(16));
  }
}
#endif

// Registers /audio-in once Wi-Fi is up. Same edge every other feature with a
// page uses; nothing here runs before the HTTP server exists.
inline void onNetwork() { PFAudioInHttp::begin(); }

inline void setup() {
  PFAudioInMap::load();
  const uint32_t before = ESP.getFreeHeap();
  // Tables and buffers only. I2S is the analysis task's business now, so a
  // panel that boots with the mic off never installs the driver at all.
  PFAudioFFT::begin();
  heapCost = before - ESP.getFreeHeap();
#if PF_AUDIO_IN_CORE == 0
  // 4 KB stack: the transform works in static buffers, so the task itself
  // needs almost nothing. Priority 1 — below Wi-Fi, above idle.
  xTaskCreatePinnedToCore(analysisTask, "pf-audio", 4096, nullptr, 1, nullptr, 0);
#endif
}

#if PF_AUDIO_IN_CORE == 1
inline void loop(const PFFeatureFrame&) {
  PFAudioFFT::analyze(tick++);
}
#endif
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
